PonderlyRobotics/esp_flipbuddy/mpu6050.py

"""
Author: Olivier Lenoir - <olivier.len02@gmail.com>
Created: 2021-12-29 14:06:10
License: MIT, Copyright (c) 2021-2022 Olivier Lenoir
Language: MicroPython v1.18
Project: MPU-6050
Description: GY-521 MPU-6050 3-axis gyroscope and acceleration sensor, InvenSense Inc.
    picocom /dev/ttyUSB0 -b 115200 | tee MPU6050raw.dat
"""

from math import acos, asin, atan2, degrees, radians, sin, sqrt

from machine import I2C, Pin
from micropython import const
from ustruct import unpack
from utime import sleep_ms

MPU6050_ADDR = const(0x68)

MPU6050_SMPRT_DIV = const(0x19)
MPU6050_CONFIG = const(0x1A)
MPU6050_INT_PIN_CFG = const(0x37)
MPU6050_INT_ENABLE = const(0x38)
MPU6050_FIFO_EN = const(0x23)
MPU6050_USER_CTRL = const(0x6A)
MPU6050_ACCEL_OUT = const(0x3B)
MPU6050_TEMP_OUT = const(0x41)
MPU6050_GYRO_OUT = const(0x43)
MPU6050_PWR_MGMT_1 = const(0x6B)
MPU6050_PWR_MGMT_2 = const(0x6C)
MPU6050_INT_STATUS = const(0x3A)
MPU6050_MEM_R_W = 0x6F  # Memory Read/Write Register

# Source and Copyright to Jeff Rowberg's MPU6050 Librar
# https://github.com/jrowberg/i2cdevlib/blob/master/ESP32_ESP-IDF/components/MPU6050/MPU6050_9Axis_MotionApps41.h
# /* ================================================================================================ *
#  | Default MotionApps v4.1 48-byte FIFO packet structure:                                           |
#  |                                                                                                  |
#  | [QUAT W][      ][QUAT X][      ][QUAT Y][      ][QUAT Z][      ][GYRO X][      ][GYRO Y][      ] |
#  |   0   1   2   3   4   5   6   7   8   9  10  11  12  13  14  15  16  17  18  19  20  21  22  23  |
#  |                                                                                                  |
#  | [GYRO Z][      ][MAG X ][MAG Y ][MAG Z ][ACC X ][      ][ACC Y ][      ][ACC Z ][      ][      ] |
#  |  24  25  26  27  28  29  30  31  32  33  34  35  36  37  38  39  40  41  42  43  44  45  46  47  |
#  * ================================================================================================ */
#
# fmt: off
# this block of memory gets written to the MPU on start-up, and it seems
# to be volatile memory, so it has to be done each time (it only takes ~1
# second though)
dmp_firmware = [
    # bank 0, 256 bytes
    0xFB, 0x00, 0x00, 0x3E, 0x00, 0x0B, 0x00, 0x36, 0x00, 0x01, 0x00, 0x02, 0x00, 0x03, 0x00, 0x00,
    0x00, 0x65, 0x00, 0x54, 0xFF, 0xEF, 0x00, 0x00, 0xFA, 0x80, 0x00, 0x0B, 0x12, 0x82, 0x00, 0x01,
    0x00, 0x02, 0x00, 0x00, 0x00, 0x00, 0x00, 0x00, 0x00, 0x00, 0x00, 0x00, 0x00, 0x00, 0x00, 0x00,
    0x00, 0x28, 0x00, 0x00, 0xFF, 0xFF, 0x45, 0x81, 0xFF, 0xFF, 0xFA, 0x72, 0x00, 0x00, 0x00, 0x00,
    0x00, 0x00, 0x03, 0xE8, 0x00, 0x00, 0x00, 0x01, 0x00, 0x01, 0x7F, 0xFF, 0xFF, 0xFE, 0x80, 0x01,
    0x00, 0x1B, 0x00, 0x00, 0x00, 0x00, 0x00, 0x00, 0x00, 0x00, 0x00, 0x00, 0x00, 0x00, 0x00, 0x00,
    0x00, 0x3E, 0x03, 0x30, 0x40, 0x00, 0x00, 0x00, 0x02, 0xCA, 0xE3, 0x09, 0x3E, 0x80, 0x00, 0x00,
    0x20, 0x00, 0x00, 0x00, 0x00, 0x00, 0x00, 0x00, 0x40, 0x00, 0x00, 0x00, 0x60, 0x00, 0x00, 0x00,
    0x41, 0xFF, 0x00, 0x00, 0x00, 0x00, 0x0B, 0x2A, 0x00, 0x00, 0x16, 0x55, 0x00, 0x00, 0x21, 0x82,
    0xFD, 0x87, 0x26, 0x50, 0xFD, 0x80, 0x00, 0x00, 0x00, 0x1F, 0x00, 0x00, 0x00, 0x05, 0x80, 0x00,
    0x00, 0x00, 0x00, 0x00, 0x00, 0x01, 0x00, 0x00, 0x00, 0x02, 0x00, 0x00, 0x00, 0x03, 0x00, 0x00,
    0x40, 0x00, 0x00, 0x00, 0x00, 0x00, 0x04, 0x6F, 0x00, 0x02, 0x65, 0x32, 0x00, 0x00, 0x5E, 0xC0,
    0x40, 0x00, 0x00, 0x00, 0x00, 0x00, 0x00, 0x00, 0x00, 0x00, 0x00, 0x00, 0x00, 0x00, 0x00, 0x00,
    0xFB, 0x8C, 0x6F, 0x5D, 0xFD, 0x5D, 0x08, 0xD9, 0x00, 0x7C, 0x73, 0x3B, 0x00, 0x6C, 0x12, 0xCC,
    0x32, 0x00, 0x13, 0x9D, 0x32, 0x00, 0xD0, 0xD6, 0x32, 0x00, 0x08, 0x00, 0x40, 0x00, 0x01, 0xF4,
    0xFF, 0xE6, 0x80, 0x79, 0x02, 0x00, 0x00, 0x00, 0x00, 0x00, 0xD0, 0xD6, 0x00, 0x00, 0x27, 0x10,

    # bank 1, 256 bytes
    0xFB, 0x00, 0x00, 0x00, 0x40, 0x00, 0x00, 0x00, 0x00, 0x00, 0x00, 0x00, 0x00, 0x00, 0x00, 0x00,
    0x00, 0x00, 0x00, 0x01, 0x00, 0x00, 0x00, 0x00, 0x00, 0x00, 0x01, 0x00, 0x01, 0x00, 0x00, 0x00,
    0x00, 0x00, 0xFA, 0x36, 0xFF, 0xBC, 0x30, 0x8E, 0x00, 0x05, 0xFB, 0xF0, 0xFF, 0xD9, 0x5B, 0xC8,
    0xFF, 0xD0, 0x9A, 0xBE, 0x00, 0x00, 0x10, 0xA9, 0xFF, 0xF4, 0x1E, 0xB2, 0x00, 0xCE, 0xBB, 0xF7,
    0x00, 0x00, 0x00, 0x01, 0x00, 0x00, 0x00, 0x04, 0x00, 0x02, 0x00, 0x02, 0x02, 0x00, 0x00, 0x0C,
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
    0xA3, 0x98, 0xF1, 0xA3, 0xA3, 0xA3, 0xA3, 0x97, 0xA3, 0xA3, 0xA3, 0xA3, 0xF3, 0x9B, 0xA3, 0xA3,
    0xDC, 0xB9, 0xA7, 0xF1, 0x26, 0x26, 0x26, 0xD8, 0xD8, 0xFF
]
# fmt: on


class MPU6050:
    """GY-521 MPU-6050 3-axis gyroscope and acceleration sensor"""

    def __init__(
        self,
        i2c,
        int_pin,
        addr=MPU6050_ADDR,
        calibrate=True,
        mean=None,
        stddev=None,
        enable_mpu=False,
    ):
        self._i2c = i2c
        self._int_pin = Pin(int_pin, Pin.IN, Pin.PULL_UP)
        self._addr = addr
        self.reset_mpu()
        self.angle_pitch = self.angle_roll = 0
        self.angle_pitch_output = self.angle_roll_output = 0
        self.set_gyro_angles = False
        self.sum = self.sum2 = [0, 0, 0, 0, 0, 0]
        self.mean = self.stddev = 0
        self._init()
        if calibrate:
            self.calibrate()
        else:
            self.mean = mean
            self.stddev = stddev

        self.irq_start(self.gyro)
        if enable_mpu:
            self.enable_dmp()

    def _init(self):
        """Init MPU6050"""
        # Power sensor
        self._i2c.writeto_mem(self._addr, MPU6050_PWR_MGMT_1, bytes([0]))
        # Set Digital Low Pass Filter (DLPF) 260Hz, Output rate 1kHz
        # self._i2c.writeto_mem(self._addr, MPU6050_CONFIG, bytes([6]))
        self._i2c.writeto_mem(self._addr, MPU6050_CONFIG, bytes([6]))
        # Set Sample Rate Divider at 64
        # Output rate: 1kHz / 64 = 15.625Hz
        # Output period: 1 / 15.625Hz = 64ms
        # self._i2c.writeto_mem(self._addr, MPU6050_SMPRT_DIV, bytes([63]))
        self._i2c.writeto_mem(self._addr, MPU6050_SMPRT_DIV, bytes([63]))
        period = 64 / 1000  # one measure every period in second
        gyro_lsb = 131  # Gyro LSB Sensitivity
        self.gyro_conv = period / gyro_lsb
        # Interrupt enable on data ready
        self._i2c.writeto_mem(self._addr, MPU6050_INT_ENABLE, bytes([1]))
        # Clear interrupt status to unlatch the interrupt pin
        self._i2c.readfrom_mem(self._addr, MPU6050_INT_STATUS, 1)

    def raw(self, _irq=None):
        """Get accel, temp and gyro raw data"""
        return unpack(
            ">hhhhhhh", self._i2c.readfrom_mem(self._addr, MPU6050_ACCEL_OUT, 14)
        )

    def raw_stdscr(self, _irq=None):
        """Get accel and gyro raw data normalize with standard score"""
        raw = list(self.raw())
        raw.pop(3)  # Pop temperature
        # Raw accel and standard score gyro
        _rms = zip(raw[3:6], self.mean[3:6], self.stddev[3:6])  # noqa: B905
        return raw[0:3] + [(r - m) / s for r, m, s in _rms]

    def calibrate(self, sample=50):
        """Calculate mean and standard deviation for accel and gyro"""
        self._i2c.writeto_mem(
            self._addr, MPU6050_USER_CTRL, b"\x00"
        )  # Disable DMP & FIFO
        self._i2c.writeto_mem(self._addr, MPU6050_FIFO_EN, b"\x00")  # Disable FIFO
        self._sample = 0
        self.sample = sample
        self.sum = self.sum2 = [0, 0, 0, 0, 0, 0]
        self.irq_start(self.mean_stddev)
        print("Calibrating", end="")
        while self._sample < self.sample:
            print(".", end="")
            sleep_ms(800)
        print()
        print("Calibration completed")
        print("    Mean:", self.mean)
        print("    StdDev:", self.stddev)

    def mean_stddev(self, _irq=None):
        """Calculate mean and standard deviation for accel and gyro"""
        raw_data = list(self.raw())
        raw_data.pop(3)  # Pop temperature
        self.sum = [rd + s for rd, s in zip(raw_data, self.sum)]  # noqa: B905
        self.sum2 = [rd**2 + s2 for rd, s2 in zip(raw_data, self.sum2)]  # noqa: B905
        self._sample += 1
        if self._sample >= self.sample:
            self.irq_stop()
            _p = self._sample
            self.mean = [s / _p for s in self.sum]
            self.stddev = [
                (s2 / _p - m**2) ** 0.5
                for m, s2 in zip(self.mean, self.sum2)  # noqa: B905
            ]

    def gyro(self, _irq=None):
        """update gyro pitch and roll"""
        raw_stdscr = self.raw_stdscr()
        accel_x, accel_y, _accel_z, gyro_x, gyro_y, gyro_z = raw_stdscr
        accel_vector = sum(a**2 for a in raw_stdscr[0:3]) ** 0.5
        # update gyro
        self.angle_pitch += gyro_x * self.gyro_conv
        self.angle_roll += gyro_y * self.gyro_conv
        yawed = sin(radians(gyro_z * self.gyro_conv))
        self.angle_pitch += self.angle_roll * yawed
        self.angle_roll -= self.angle_pitch * yawed
        # Accelerometer angle
        angle_pitch_accel = degrees(asin(accel_y / accel_vector))
        angle_roll_accel = -degrees(asin(accel_x / accel_vector))
        if self.set_gyro_angles:
            # Drift correction
            self.angle_pitch = self.angle_pitch * 0.98 + angle_pitch_accel * 0.02
            self.angle_roll = self.angle_roll * 0.98 + angle_roll_accel * 0.02
        else:
            # Gyro origin based on gravity
            self.angle_pitch = angle_pitch_accel
            self.angle_roll = angle_roll_accel
            self.set_gyro_angles = True
        # Complementary filter
        self.angle_pitch_output = self.angle_pitch_output * 0.9 + self.angle_pitch * 0.1
        self.angle_roll_output = self.angle_roll_output * 0.9 + self.angle_roll * 0.1

    def tilt(self, _irq=None):
        """Tri-axis tilt sensing using 3-axis accelerometer"""
        raw_accel = list(self.raw())[0:3]
        _g = sum(a**2 for a in raw_accel) ** 0.5
        return [degrees(f(a / _g)) for a, f in zip(raw_accel, (asin, asin, acos))]  # noqa: B905

    def tilt_refin(self, _irq=None):
        """Compute both normalized acceleration-based tilt and roll/pitch angles. Eulor's formula."""
        raw_accel = list(self.raw())[0:3]
        _g = sum(a**2 for a in raw_accel) ** 0.5
        tilt_x, tilt_y, tilt_z = [
            degrees(f(a / _g))
            for a, f in zip(raw_accel, (asin, asin, acos))  # noqa: B905
        ]
        x, y, z = [a / 16384 for a in raw_accel]  # +-2G
        roll = degrees(atan2(y, z))
        pitch = degrees(atan2(x, sqrt(y**2 + z**2)))
        return (tilt_x, tilt_y, tilt_z, x, y, z, roll, pitch)

    def irq_start(self, func):
        """Start IRQ"""
        self._int_pin.irq(trigger=Pin.IRQ_FALLING, handler=func)

    def irq_stop(self):
        """Stop IRQ"""
        self._int_pin.irq(trigger=Pin.IRQ_FALLING)

    def all(self):
        x, y, z = self.tilt()
        return (x, y, z, self.angle_roll_output, self.angle_pitch_output)

    def low_power_mode(self):
        """Put MPU6050 into low power mode."""
        # Set sleep mode and disable gyroscope (bit 5 = 1)
        # https://invensense.tdk.com/wp-content/uploads/2015/02/MPU-6000-Register-Map1.pdf
        self._i2c.writeto_mem(
            self._addr, MPU6050_PWR_MGMT_1, bytes([0x48])
        )  # b'01001000'
        print("MPU6050 is now in low power mode.")

    def register_irq_function(self, func):
        """Register an external function to be called when the interrupt triggers."""
        self._int_pin.irq(trigger=Pin.IRQ_FALLING, handler=func)
        print("New IRQ function registered.")

    def enable_motion_detection(self, threshold=10, trigger_pin=2):
        """
        Enable motion detection with DMP-enabled interrupts.

        Args:
            threshold (int): Sensitivity threshold for motion detection.
            trigger_pin (int): Pin number to trigger when motion is detected.
        """
        self._i2c.writeto_mem(self._addr, MPU6050_USER_CTRL, b"\x04")  # Reset DMP FIFO

        # Enable motion detection in DMP (Interrupt & FIFO)
        self._i2c.writeto_mem(
            self._addr, MPU6050_INT_PIN_CFG, b"\x20"
        )  # Latch INT signal
        self._i2c.writeto_mem(
            self._addr, MPU6050_FIFO_EN, b"\x08"
        )  # Enable FIFO for accel
        self._i2c.writeto_mem(
            self._addr, MPU6050_INT_ENABLE, bytes([0x40])
        )  # Bit 6: Motion Interrupt Enable
        self._i2c.writeto_mem(
            self._addr, 0x1F, bytes([threshold])
        )  # MOT_THR register (1 LSB = 1mg)
        self._i2c.writeto_mem(
            self._addr, 0x20, bytes([1])
        )  # MOT_DUR register (time window)
        self._i2c.writeto_mem(
            self._addr, MPU6050_USER_CTRL, b"\x44"
        )  # Enable DMP + FIFO

        def motion_detected(_irq):
            self._i2c.readfrom_mem(self._addr, MPU6050_INT_STATUS, 1)

        self.register_irq_function(motion_detected)
        print(f"✅ DMP Motion Detection Enabled (Threshold: {threshold})")

    def enable_low_power_dmp_motion_detection(self, threshold=2, sample_rate_div=16):
        """
        Enable DMP motion detection in Low Power Mode.
        Args:
            threshold (int): Sensitivity threshold for motion detection (1 LSB = 1mg).
            sample_rate_div (int): Lower sample rate to reduce power consumption.
        """
        print("🔋 Enabling Low Power Mode with DMP Motion Detection...")

        self._i2c.writeto_mem(
            self._addr, MPU6050_USER_CTRL, b"\x04"
        )  # Reset DMP FIFO & Motion Detection
        self._i2c.writeto_mem(
            self._addr, MPU6050_INT_PIN_CFG, b"\x20"
        )  # Latch INT signal
        self._i2c.writeto_mem(
            self._addr, MPU6050_FIFO_EN, b"\x08"
        )  # Enable FIFO for accel only
        self._i2c.writeto_mem(
            self._addr, MPU6050_INT_ENABLE, bytes([0x40])
        )  # Enable Motion Interrupt
        self._i2c.writeto_mem(
            self._addr, 0x1F, bytes([threshold])
        )  # MOT_THR register (1 LSB = 1mg)
        self._i2c.writeto_mem(
            self._addr, 0x20, bytes([1])
        )  # MOT_DUR register (time window)
        self._i2c.writeto_mem(
            self._addr, MPU6050_SMPRT_DIV, bytes([sample_rate_div])
        )  # Reduce sample rate
        self._i2c.writeto_mem(
            self._addr, MPU6050_USER_CTRL, b"\x44"
        )  # Enable DMP and FIFO again
        self._i2c.writeto_mem(
            self._addr, MPU6050_PWR_MGMT_1, b"\x29"
        )  # Cycle mode (Keep DMP alive)
        self._i2c.writeto_mem(
            self._addr, MPU6050_PWR_MGMT_2, b"\x47"
        )  # Disable Gyro (only accelerometer)
        self._i2c.readfrom_mem(
            self._addr, MPU6050_INT_STATUS, 1
        )  # clear firs interrupt

        print(f"✅ Low Power DMP Motion Detection Enabled (Threshold: {threshold})")

    def configure_for_deep_sleep(self, threshold=2, sample_rate_div=16):
        """Dedicated deep sleep config (called by prepare_for_deep_sleep).

        Puts MPU6050 into the low power + DMP motion detect state used
        to wake via ext0/PIN_WAKE while drawing minimal current.
        """
        self.enable_low_power_dmp_motion_detection(
            threshold=threshold, sample_rate_div=sample_rate_div
        )
        try:  # noqa: SIM105
            self._i2c.readfrom_mem(self._addr, MPU6050_INT_STATUS, 1)
        except Exception:
            pass

    def upload_dmp_firmware(self):
        """Uploads the DMP firmware to the MPU6050."""
        print("Uploading DMP Firmware...")

        # Reset MPU6050 and enable memory write mode
        self._i2c.writeto_mem(self._addr, MPU6050_PWR_MGMT_1, b"\x80")  # Reset device
        sleep_ms(100)
        self._i2c.writeto_mem(self._addr, MPU6050_PWR_MGMT_1, b"\x00")  # Wake up
        sleep_ms(10)
        self._i2c.writeto_mem(self._addr, MPU6050_USER_CTRL, b"\x04")  # Reset FIFO
        sleep_ms(10)

        for _, byte in enumerate(dmp_firmware):
            self._i2c.writeto_mem(
                self._addr, MPU6050_MEM_R_W, bytes([byte])
            )  # Write to MPU RAM
            sleep_ms(1)

    def is_dmp_active(self):
        """Check if DMP is currently enabled."""
        user_ctrl = self._i2c.readfrom_mem(self._addr, MPU6050_USER_CTRL, 1)
        return bool(user_ctrl[0] & 0x80)  # Bit 7: DMP Enabled

    def enable_dmp(self):
        """Enables the DMP feature in the MPU6050."""
        print("Enabling DMP...")
        self._i2c.writeto_mem(self._addr, MPU6050_PWR_MGMT_1, b"\x80")  # Reset device
        sleep_ms(100)
        self._i2c.writeto_mem(self._addr, MPU6050_PWR_MGMT_1, b"\x00")  # Wake up
        sleep_ms(10)
        self._i2c.writeto_mem(self._addr, MPU6050_USER_CTRL, b"\x04")  # Reset FIFO
        sleep_ms(10)

        self._i2c.writeto_mem(self._addr, MPU6050_USER_CTRL, b"\x40")  # Enable DMP
        self._i2c.writeto_mem(self._addr, MPU6050_USER_CTRL, b"\x44")  # Enable FIFO
        print("DMP Enabled.")

    def reset_mpu(self):
        """Fully reset the MPU6050 to its default configuration."""
        print("🔄 Resetting MPU6050 to default settings...")
        self._i2c.writeto_mem(
            self._addr, MPU6050_PWR_MGMT_1, b"\x80"
        )  # Reset bit (bit 7)
        sleep_ms(50)  # giving mpu6050 time to reset fully
        self._i2c.writeto_mem(self._addr, MPU6050_PWR_MGMT_1, b"\x00")
        self._i2c.writeto_mem(self._addr, MPU6050_PWR_MGMT_2, b"\x00")
        self._i2c.writeto_mem(
            self._addr, MPU6050_USER_CTRL, b"\x00"
        )  # Disable FIFO & DMP
        self._i2c.writeto_mem(
            self._addr, MPU6050_INT_ENABLE, b"\x00"
        )  # Disable Interrupts
        self._i2c.writeto_mem(self._addr, 0x1F, b"\x00")  # MOT_THR
        self._i2c.writeto_mem(self._addr, 0x20, b"\x00")  # MOT_DUR
        self._i2c.readfrom_mem(self._addr, MPU6050_INT_STATUS, 1)  # Unlatch Int pin
        print("✅ MPU6050 has been reset!")


def cube_face_upward(sensor: MPU6050, margin=0.2, angle_margin=10):
    """
    Enhanced face detection using acceleration-based tilt + roll/pitch.

    Args:
        sensor (MPU6050): The MPU6050 sensor instance.
        margin (float): Allowed margin for acceleration-based detection.
        angle_margin (float): Allowed margin for roll/pitch (default 10°).

    Returns:
        str: The name of the upward-facing face.
    """
    # Get all sensor data: tilt angles, acceleration values, roll & pitch
    tilt_x, tilt_y, tilt_z, x, y, z, roll, pitch = sensor.tilt_refin()

    # 1. Cutout Detection Using Roll & Pitch**
    if (115 <= roll <= 145) and (-50 <= pitch <= -30):
        return "back_cutout"
    elif (-60 <= roll <= -20) and (20 <= pitch <= 40):
        return "front_cutout"

    # 2. Face Detection Using Acceleration (Gravity)**
    # Renamed faces: back→front, left→bottom, front→back, bottom→left, right→top, top→right
    if -margin <= x <= margin and -margin <= y <= margin:
        return "left" if z > 0 else "right"  # was bottom / top
    elif -margin <= y <= margin and -margin <= z <= margin:
        return "bottom" if x > 0 else "top"  # was left / right
    elif -margin <= x <= margin and -margin <= z <= margin:
        return "front" if y > 0 else "back"  # was back / front

    # 3. Additional Tilt Detection (Using asin/acos Method)**
    # If the tilt angles indicate the cube is **not aligned** with any face
    if abs(tilt_x) > 90 or abs(tilt_y) > 90 or abs(tilt_z) > 90:
        return "out_margin"

    # 4. Roll & Pitch Refinement**
    if abs(roll) > angle_margin or abs(pitch) > angle_margin:
        return "out_margin"

    return "unknown"


def print_orinetation(sensor: MPU6050, frequency: int = 10):
    while True:
        print(sensor.pprint_raw(), f"\tFace: {cube_face_upward(sensor)}")
        sleep_ms(int(1000 / frequency))


def sensor_init(
    calibrate=True,
    mean=None,
    stddev=None,
    enable_mpu=False,
    sda_pin=11,
    scl_pin=12,
    intruppt_pin=10,
):
    # Do not wrap runtime args in micropython.const() — that requires compile-time
    # constants and raises SyntaxError: not a constant on stock MicroPython.
    i2c_bus = I2C(0, scl=Pin(scl_pin), sda=Pin(sda_pin), freq=400000)
    detector = MPU6050(
        i2c_bus,
        intruppt_pin,
        calibrate=calibrate,
        mean=mean,
        stddev=stddev,
        enable_mpu=enable_mpu,
    )
    return detector
